Synapseware/enterprise/core/effects.h

#ifndef __EFFECTS_H__
#define __EFFECTS_H__


#include <avr/interrupt.h>
#include <avr/pgmspace.h>
#include <avr/eeprom.h>
#include <string.h>

#include <events/events.h>
#include <uart/uart.h>
#include <at24c/at24c.h>

#include "board.h"
#include "enterprise.h"



// playback rate, in Hz
static const uint16_t	SAMPLE_RATE			= 8000;
static const uint8_t	SAMPLE_LOADING		= 0xEE;
static const uint8_t	SAMPLE_PLAYING		= 0xFF;
static const uint8_t	SAMPLE_NONE			= 0x00;
static const uint8_t	SFX_OFF				= 0x00;
static const uint8_t	SFX_ON				= 0xFF;

static const uint8_t	SFX_RESULT_SUCCESS	= 0;

static const uint16_t   effectsStart		= 0x00;	 // start address of effects records in EEPROM

static const uint8_t	RT_NULL				= 0xFF;	 // null record
static const uint8_t	RT_SOUND			= 0x01;	 // sound effects
static const uint8_t	RT_LIGHT			= 0x02;	 // lighting effects
static const uint8_t	RT_MOTION			= 0x04;	 // motion effects
static const uint8_t	RT_FIXED			= 0x08;	 // fixed schedule (not set implies a random scheduling)


// - - - - - - - - - - - - - - - - - - - - - - - - - - - - - - - - - - - - - - - - - - -  - -
// Header structure...
//	0	0x02	2		Signature
//	1
//	2	0x04	2		Start Page
//	3
//	4	0x06	2		Total Pages
//	5
//	6	0x08	1		Bytes Used In Last Page
//	7			1		Reserved
//	8	0x0A	2		Sample Rate
//	9
//	A	start of next entry...

// SOUND_EFFECT reflects an individual entry in the header record
typedef struct
{
	uint16_t		startPage;				// + 2		2
	uint32_t		length;					// + 4		4
} volatile SOUND_EFFECT;					// 6 bytes

// SOUND_HEADER reflects the actual header record
typedef struct
{
	uint16_t          samples;              // + 0	// # of samples (0-255)
	SOUND_EFFECT      effects[42];          // + 2	// array of sound effects
} SOUND_HEADER;                    			// 2 + 42 * 6 bytes = 254 bytes

	void renderAudioData(void);


// - - - - - - - - - - - - - - - - - - - - - - - - - - - - - - - - - - - - - - - - - - -  - -
// Sound effects methods
void efx_renderAudioData(void);
int efx_init(Events* events);
void efx_on(void);
void efx_off(void);
uint8_t efx_playing(void);
void efx_startSample(uint8_t index);


// - - - - - - - - - - - - - - - - - - - - - - - - - - - - - - - - - - - - - - - - - - -  - -
// ambient sounds
static const uint8_t SFX_AMBIENT_BEEP_BEEP		= 0;
static const uint8_t SFX_AMBIENT_BEEP_UP		= 1;
static const uint8_t SFX_AMBIENT_KEY_BEEP		= 2;
static const uint8_t SFX_AMBIENT_WHIP_WHIP		= 3;

// background sounds
static const uint8_t SFX_BK_ASTROGATOR			= 4;
static const uint8_t SFX_BK_MAIN_SCREEN			= 5;

// sound effects
static const uint8_t SFX_EFX_COMM				= 6;
static const uint8_t SFX_EFX_DOORS				= 7;
static const uint8_t SFX_EFX_ENERGIZE			= 8;
static const uint8_t SFX_EFX_HAILING			= 9;
static const uint8_t SFX_EFX_HEART				= 10;
static const uint8_t SFX_EFX_OPENING			= 11;
static const uint8_t SFX_EFX_RED_ALERT			= 12;
static const uint8_t SFX_EFX_REPLICATOR			= 13;
static const uint8_t SFX_EFX_TRIBBLE			= 14;

// voices
static const uint8_t SFX_VOICES_DOCTOR			= 15;
static const uint8_t SFX_VOICES_IMPOSSIBLE		= 16;
static const uint8_t SFX_VOICES_BRIDGE_KIRK		= 17;
static const uint8_t SFX_VOICES_WHAT_DO			= 18;
static const uint8_t SFX_VOICES_GOING_DOWN		= 19;
static const uint8_t SFX_VOICES_BEAM_ME_UP		= 20;
static const uint8_t SFX_VOICES_KIRK_HERE		= 21;
static const uint8_t SFX_VOICES_AYE_SIR			= 22;
static const uint8_t SFX_VOICES_SCOTTY_KIRK		= 23;
static const uint8_t SFX_VOICES_FASCINATING		= 24;


const static uint8_t AMBIENT_SOUND[] PROGMEM = {
    0x7C, 0x78, 0x75, 0x71, 0x6E, 0x6B, 0x67, 0x65, 0x62, 0x60, 0x5E, 0x5C, 0x5B, 0x5A, 0x5A, 0x5B, 0x5B, 0x5C, 0x5E, 0x5F,
    0x61, 0x63, 0x64, 0x66, 0x67, 0x69, 0x6A, 0x6B, 0x6D, 0x6E, 0x70, 0x72, 0x74, 0x76, 0x78, 0x7A, 0x7D, 0x7F, 0x82, 0x84,
    0x86, 0x88, 0x89, 0x8A, 0x8B, 0x8B, 0x8A, 0x89, 0x87, 0x85, 0x82, 0x7F, 0x7B, 0x78, 0x74, 0x70, 0x6D, 0x6A, 0x68, 0x66,
    0x65, 0x64, 0x64, 0x65, 0x66, 0x67, 0x68, 0x69, 0x6A, 0x6A, 0x6B, 0x6C, 0x6C, 0x6D, 0x6D, 0x6E, 0x6E, 0x70, 0x71, 0x73,
    0x75, 0x78, 0x7A, 0x7D, 0x81, 0x84, 0x87, 0x89, 0x8C, 0x8E, 0x90, 0x91, 0x92, 0x92, 0x92, 0x92, 0x92, 0x92, 0x91, 0x91,
    0x90, 0x8F, 0x8E, 0x8C, 0x8A, 0x88, 0x85, 0x82, 0x7E, 0x7B, 0x77, 0x73, 0x6F, 0x6C, 0x69, 0x67, 0x65, 0x64, 0x63, 0x63,
    0x63, 0x64, 0x66, 0x69, 0x6C, 0x70, 0x75, 0x7A, 0x80, 0x86, 0x8C, 0x93, 0x99, 0x9F, 0xA5, 0xAB, 0xB0, 0xB5, 0xBA, 0xBE,
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
    0x7C, 0x7A, 0x79, 0x78, 0x77, 0x77, 0x77, 0x77, 0x78, 0x7A, 0x7B, 0x7D, 0x80, 0x82, 0x85, 0x87, 0x8A, 0x8C, 0x8F, 0x91,
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
};
static const uint16_t AMBIENT_LEN = sizeof(AMBIENT_SOUND)/sizeof(uint8_t);


#endif
